fook42/1541-rePico/doc/pictures/IMG_20260502_215122.jpg

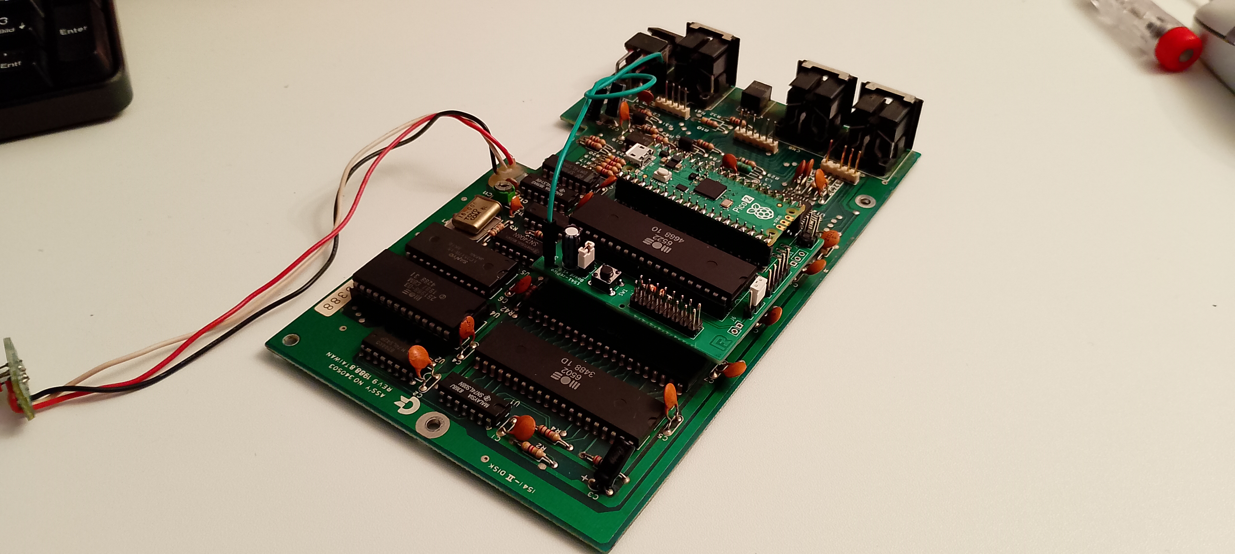
doc/pictures/IMG_20260502_215122.jpg
