fook42/1541-rePico/doc/pictures/1541DiagTest.jpg

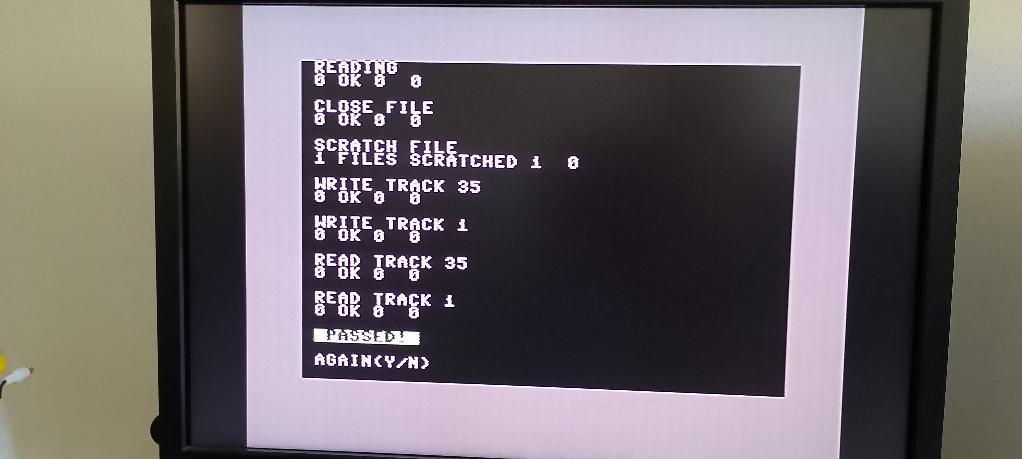
doc/pictures/1541DiagTest.jpg
