fook42/1541-rePico/firmware/SoftwareC64/menu.asm

        ;!to "menu.prg",cbm

        !cpu 6510

;   Typ [8bit, 1 =file, 2=dir], 
;   Filename[chars],stopbyte[8bit, =0] .. jeweils pro eintrag hintereinander
    TYPE_NONE = 0
    TYPE_DIR = 1
    TYPE_D64 = 2
    TYPE_G64 = 3
    TYPE_PRG = 4
    TYPE_UNKNOWN = 255


!ifdef VIC20 {
    MAX_X = 22	    ;screen width
    MAX_LINE = 21


    VIDEORAM = $1000
    COLORRAM = $9400
    E518 = $E55F
    BORDER_COLOR = $04
    SELECTOR_COLOR = $0a
    LOAD = $ffd5
    BA = $ba
    ptr1 = $fb
    ptr2 = $fd
    ptr3 = $f7
    D020 = $900f

} else  { ; VIC20

    MAX_X = 40	    ;screen width
    MAX_LINE = 23

    
!ifdef C16 {
    VIDEORAM = $0c00
    COLORRAM = $0800
    RASTER_LINE = $ff0b
    RASTER_LINE_READ = $ff1d
    VIC_IRQ_ENA = $ff0a
    VIC_IRQ_STATUS = $ff09
    EA31 = $ce0e
    E518 = 55435
    D020 = $ff19
    D021 = $ff15
    BORDER_COLOR = $3b
    SELECTOR_COLOR = $18
    LOAD = $ffd5
    BA = $0137
    ptr1 = $03
    ptr2 = $05
    ptr3 = $9f

} else {
    VIDEORAM = $0400
    COLORRAM = $d800
    RASTER_LINE = $d012
    RASTER_LINE_READ = $d012
    VIC_IRQ_ENA = $d01a
    VIC_IRQ_STATUS = $d019
    EA31 = $ea31
    E518 = $e518
    D020 = $d020
    D021 = $d021
    BORDER_COLOR = $0b
    SELECTOR_COLOR = $02
    BA = $ba
    !ifdef NTSC {
    LOAD = FASTLOAD_EXOS
    } else {
    LOAD = $014b
    }
    ptr1 = $fb
    ptr2 = $fd
    ptr3 = $f7
}
} ; VIC20

    STACK_START = $0138

tmp1 = $02
tmp2 = $ff
directory_end = $ae
x_pos = $92

current_pos = $c1
current_endpos = $c3

current_cursor_position = $9e
!ifdef VIC20 {
current_cursor_last_position = $9f
}

current_index_number = $ac

DRIVECODE_START = $0146

TOGGLE_DISKWRITE_FOR_DISKSWITCH = 2

;CLEANUP_BLOCK_WRITTEN = 1
DRIVE_RESET = 1;
	!ifndef NTSC {
DRIVE_INITIALIZE = 1
	}



LINE_SIZES = $033c  ;"MAX_LINE"-bytes to line lengths


!macro dec_word .x {
        lda .x
        bne +
        dec .x+1
+       dec .x
        }

!macro inc_word .x {
        inc .x
        bne +
        inc .x+1
+
}

!macro conv_to_screen {
        cmp #$5f
        bne +
        lda #$64
        bne .store_code
+
        cmp #$60
        bcc .store_code
        sbc #$20
.store_code:
        }
        ;rts

        !ifdef VIC20 {
        *= $1201
        !by $0b,$12,$00,$00,$9e,$34,$36,$32,$31,$00,$00,$00
        } else {
        !ifndef C16 {
        * = $0808
        } else {
        * = $1008
        }
        }
        jsr fastload_init
        !ifdef VIC20 {
        } else { ; VIC20
        !ifdef C16 {
        lda #$08
        sta BA
        } else {
        dec $01
        }
        } ; VIC20
restart:
        jsr load_menu_file
        !ifdef VIC20 {
        lda #$02
        sta current_cursor_last_position
        }        
        jsr E518
        ldy #MAX_X
-       lda buttomline-1,y
        ora #$80
        sta VIDEORAM+(MAX_LINE+1)*MAX_X-1,y
        lda #BORDER_COLOR
        sta COLORRAM-1,y
        sta COLORRAM+(MAX_LINE+1)*MAX_X-1,y
        dey
        bne -
        !ifdef VIC20 {
        lda #BORDER_COLOR+8
        sta $900f
        } else { ; VIC20
        sta D020
        sty D021
        }
        !ifdef C16 {
        lda #$39
        } else {
        lda #$1b
        sta $d011
        }
        !ifdef VIC20 {
        lda #$c2
        sta $9005
        } else {   ; VIC20
        sta RASTER_LINE
        !ifdef C16 {
        lda #$d5
        sta $ff13
        } else {
        lda #$17
        sta $d018
        lda #$7f
        sta $dc0d
        lda $dc0d
        }
        lda #<irq
        sta $0314
        lda #>irq
        sta $0315
        !ifdef C16 {
        lda #$02
        } else {
        lda #$81
        sta VIC_IRQ_ENA
        }
        !ifdef C16 {
        sta VIC_IRQ_STATUS
        } else {
        inc VIC_IRQ_STATUS
        }
        }  ; VIC20

        ;ldy #<directory_start  ; is zero now
        sty ptr1
        lda #>directory_start
        sta ptr1+1
        sta current_pos+1
-       lda (ptr1),y
        beq end_of_top_line_string
        +conv_to_screen
        ora #$80
        sta VIDEORAM,y
        iny
        cpy #MAX_X
        bne -
        dey
-       iny
        lda (ptr1),y
        bne -
end_of_top_line_string:
        tya
        tax
-       cpx #MAX_X
        bcs end_top_line
        lda #$a0
        sta VIDEORAM,x
        inx
        bne -
end_top_line:
        ;tya
        ;sec
        ;adc #<directory_start
        ;sta current_pos
        iny
        sty  current_pos
        ;lda #$00
        ;adc #>directory_start
        ;lda #>directory_start
        ;sta current_pos+1

        jsr calc_at_current_pos
        ldx tmp1
        stx maxline_cmp_value_calc_sizes
        beq +
        dex
+       stx maxline_cmp_value

repaint:
        jsr print_at_current_pos
        !ifdef VIC20 {
        ldx current_cursor_position
        beq +
        dex
        !byte $89
+       inx
        stx current_cursor_last_position
        }
keyloop:
        !ifdef VIC20 {
        jsr set_scroll_bar
        }
        jsr $ffe4
        beq keyloop
        cmp #17    ;cursor down
        bne no_cursor_down
        lda current_cursor_position
maxline_cmp_value = *+1
        cmp #MAX_LINE-1
        bcc do_cursor_down
        jsr try_scroll_down
        jmp repaint
do_cursor_down:
        inc current_cursor_position
        jmp keyloop

no_cursor_down:
        cmp #145    ;cursor up
        bne no_cursor_up
        lda current_cursor_position
        beq do_scroll_up
        dec current_cursor_position                
        jmp keyloop
do_scroll_up:
        jsr try_scroll_up
        jmp repaint

no_cursor_up:
        cmp #136    ;f7
        bne no_f7
        lda #MAX_LINE
-       pha
        jsr try_scroll_down
        bcc +
        jsr calc_at_current_pos
+       pla
        sec
        sbc #$01
        bne -
        jmp repaint

no_f7:  cmp #133    ;f1
        bne no_f1
        lda #MAX_LINE
-       pha
        jsr try_scroll_up
        bcc +
        jsr calc_at_current_pos
+       pla
        sec
        sbc #$01
        bne -
        jmp repaint

no_f1:  cmp #29     ;cursor right
        bne no_crsr_right
        lda x_pos
        cmp #255-MAX_X
        bcs keyloop
        inc x_pos
        jmp repaint
        
no_crsr_right:
        cmp #157    ;cursor left
        bne no_crsr_left
        lda x_pos
        beq keyloop
        dec x_pos
        jmp repaint
        
no_crsr_left:
        cmp #$13    ; home
        bne no_home
        lda #$00
        sta x_pos
        jmp repaint

no_home:
        cmp #134
        bne no_f3
        !ifdef VIC20 {
        lda #$2c
        sta skip_vic20_fastload
        jmp do_space
        } else { ; VIC20
        !ifdef C16 {
        ldx #$2c
        stx fastload_c16_deactivated
        bne do_space
        } else {
        !ifdef NTSC {
        lda #$24
        sta fix_for_normal_load_ntsc
        bne do_space    ;unconditional	
        } else {
        inc fix_for_normal_load2
        dec fix_for_normal_load3
        lda #$4c
        sta fix_for_normal_load
        lda #<$ffd5 
        sta fix_for_normal_load+1
        lda #>$ffd5 
        sta fix_for_normal_load+2
        bne do_space    ;unconditional
        }
        }
        } ; VIC20
no_f3:       
        cmp #$20
        beq do_space

        cmp #$0d    ;return
        beq do_space
do_keyloop:
        jmp keyloop
do_space:
        sbc #$20
        sta do_run
        jsr get_current_type
        sta current_type
        cmp #TYPE_PRG+1
        bcs do_keyloop
        cmp #TYPE_DIR
        bcc do_keyloop
        lda #$00
        !ifdef VIC20 {
        } else { ; VIC20
        !ifdef C16 {
        lda #$cc
        sta RASTER_LINE
        lda #$02
        sta VIC_IRQ_STATUS
        } else {
        sta VIC_IRQ_ENA
        inc VIC_IRQ_STATUS
        }
        lda #<EA31
        sta $0314
        lda #>EA31
        sta $0315
        !ifdef C16 {
        } else {
        lda #$81
        sta $dc0d
        }
        ;lda $dc0d
        } ; VIC20
        
        lda current_cursor_position
        ;sec        ; carry is set because no "bcc do_keyloop"
        adc current_index_number
        sta index
        lda current_index_number+1
        adc #$00
        sta index+1

        jsr upload_code
        !ifdef CLEANUP_BLOCK_WRITTEN {
        jsr clear_buffer_2
        }
        jsr block_write
        jsr wait_for_flipdisk
        !ifdef VIC20 {
        } else {
        !ifdef DRIVE_RESET {
        jsr drive_initialize
        }
        }
current_type = *+1
        lda #$00
        cmp #TYPE_DIR
        bne +
        jmp restart
+        
        !ifdef C16 {
        sei
        sta $FF3E
        ldx #$ff
        txs
        jsr 55373   ;editor reset
        jsr 62219   ;io init
        jsr 62158   ;restore vectors
        lda #$00
        sta $fdd0 
        cli
        }
do_run = *+1
        lda #$00
        beq do_exit
        !ifdef C16 {
        ;jsr drive_reset
        ;jsr 32814   ;basic reset
fastload_c16_deactivated:
        jsr $0700
        ldx #load_run_text_len
        stx $ef
        } else {
        ldx #load_run_text_len
        stx $c6
        }
        sei
-       lda load_run_text-1,x
        !ifdef C16 {
        sta $0527-1,x
        } else { 
        sta $0277-1,x
        }
        dex
        bne -
do_exit:
        !ifdef VIC20 {
        ldx #$00
        ldy #$00
-       inx
        bne -
        iny
        bne -
        jmp $fd35   ;jump to basic warm start
        } else { ; VIC20
        !ifdef C16 {
        jsr 32962   ;init screen
        cli
        ;jmp ($0302)
        jmp 32778   ;basic warm start
        } else {
        ;lda #$37
        inc $01
        ;jsr $E422
        ;cli
        ;jmp $a474
        jsr $fda3
        jmp $fcf8   ;part of reset, jumps to ($a000)
        }
        } ; VIC20

        !ifndef VIC20 {
irq:    ldy #SELECTOR_COLOR
        !ifndef C16 {
        lda RASTER_LINE_READ
-       cmp RASTER_LINE_READ
        beq -
        }
        sty D021
        lda #<irq2
        sta $0314
        ;lda #>irq2
        ;sta $0315
current_cursor_position_this_irq = *+1
        lda #$00
        clc
        !ifdef C16 {
        adc #$12
        } else {
        adc #$42
        }
        sta RASTER_LINE

        lda current_cursor_position
        asl
        asl
        asl
        sta current_cursor_position_this_irq
        sta current_cursor_position_other_irq
        !ifdef C16 {
        lda #$02
        sta VIC_IRQ_STATUS
        } else {
        inc VIC_IRQ_STATUS
        dec $028B
        bne +
        inc $028B
+
        }
        !ifdef C16 {
        jmp c16irqcont
        } else {
        jmp $ea81
        }

irq2:
        ldy #$03
-       dey
        bne -
        sty D021
        lda #<irq
        sta $0314
        ;lda #>irq
        ;sta $0315
current_cursor_position_other_irq = *+1
        lda #$00
        clc
        !ifdef C16 {
        adc #$a
        } else {
        adc #$39
        }
        sta RASTER_LINE
        !ifdef C16 {
        lda #$02
        sta VIC_IRQ_STATUS
c16irqcont:
        cli
        jsr $DB11       ;tastatur abfragen
        pla
        tay
        pla
        tax
        pla
        rti
        } else {
        inc VIC_IRQ_STATUS
        jmp EA31
        }

    !if >irq2 != >irq {
        !error "irq and irq in different pages"
    }
    }   ;!ifndef VIC20 

get_current_type:
        lda current_pos
        sta ptr1
        lda current_pos+1
        sta ptr1+1
        ldx #$00
        beq get_current_type_loop ;unconditional
--      inx
        ldy #$00
-       iny
        lda (ptr1),y
        bne -
        tya
        sec
        adc ptr1
        sta ptr1
        bcc +
        inc ptr1+1
+
        
get_current_type_loop:
        cpx current_cursor_position
        bne --
        ldy #$00
        lda (ptr1),y
        rts

calc_at_current_pos:
        lda current_pos
        sta ptr1
        lda current_pos+1
        sta ptr1+1
        lda #$00
        sta tmp1
calc_big_loop:
        lda ptr1
        cmp directory_end
        lda ptr1+1
        sbc directory_end+1
        bcs end_calcing

        ldy #$ff
-       iny
        lda (ptr1),y
        bne -
        tya
        sec
        adc ptr1
        sta ptr1
        bcc +
        inc ptr1+1
+
        inc tmp1
        lda tmp1
        cmp #MAX_LINE
        bne calc_big_loop
end_calcing:
        jmp end_printing


print_at_current_pos:
        ;cal line sizes
        lda current_pos
        sta ptr1
        lda current_pos+1
        sta ptr1+1
        ldx #$ff
--      
        ldy #$00
        inx
maxline_cmp_value_calc_sizes = *+1
        cpx #00
        beq print_at_current_pos_continue
        dey
-       iny
        lda (ptr1),y
        bne -
        tya
        sta LINE_SIZES,x
        sec
        adc ptr1
        sta ptr1
        bcc --
        inc ptr1+1
        bne --

print_at_current_pos_continue:        
        ;print
        
        lda #<LINE_SIZES
        sta line_size

        lda current_pos
        sta ptr1
        lda current_pos+1
        sta ptr1+1
        lda #$00
        sta tmp1
        lda #MAX_X
        sta ptr2
        sta ptr3
        lda #>VIDEORAM
        sta ptr2+1
        lda #>COLORRAM
        sta ptr3+1
print_big_loop:
        lda ptr1
        cmp directory_end
        lda ptr1+1
        sbc directory_end+1
        bcc +
        jmp end_printing
+
        ldy #$00
        lax (ptr1),y
        inx
        +inc_word ptr1        

        lda x_pos
line_size = *+1
        cmp LINE_SIZES
        bcc do_print
-       lda (ptr1),y
        beq +
        iny
        bne -
+       sty tmp2
        ldy #$00
        lda #$20
-       sta (ptr2),y
        !ifdef VIC20 {
        lda filetypecolor,x        
        sta (ptr3),y
        lda #$20       
        }
        iny
        cpy #MAX_X
        bne -
        ldy tmp2
        jmp end_line

do_print:
        lda x_pos
        clc
        adc ptr1
        sta ptr1
        bcc +
        inc ptr1+1
+        
-       lda (ptr1),y
        beq string_ends
        +conv_to_screen
        sta (ptr2),y
        lda filetypecolor,x
        sta (ptr3),y
        iny
        cpy #MAX_X
        bne -
        ;find end of string
-       lda (ptr1),y
        beq end_line
        iny
        bne -
        ;!byte $02
string_ends:
        sty tmp2
        lda #$20
-       sta (ptr2),y
        !ifdef VIC20 {
        lda filetypecolor,x        
        sta (ptr3),y
        lda #$20       
        }
        iny
        cpy #MAX_X
        bne -
        ldy tmp2
end_line:
        tya
        sec
        adc ptr1
        sta ptr1
        bcc +
        inc ptr1+1
        clc
+       lda ptr2
        adc #MAX_X
        sta ptr2
        sta ptr3
        bcc +
        inc ptr2+1
        inc ptr3+1
+       inc line_size
        inc tmp1
        lda tmp1
        cmp #MAX_LINE
        beq end_printing
        jmp print_big_loop
end_printing:
        lda ptr1
        sta current_endpos
        lda ptr1+1
        sta current_endpos+1
        rts

!macro current_pos_equ_ptr1_plus_1 {
        lax ptr1
        sbx #$100-$01
        stx current_pos
        lda ptr1+1
        adc #$00
        sta current_pos+1
        }

try_scroll_up:
        lda current_index_number
        ora current_index_number+1
        beq try_scroll_up_failed
        lax current_pos
        sbx #$02
        stx ptr1
        lda current_pos+1
        sbc #$00
        sta ptr1+1
        ldy #$00
        jmp try_scroll_up_do_search
-
        +dec_word ptr1
try_scroll_up_do_search:
        lda (ptr1),y
        bne -
        +current_pos_equ_ptr1_plus_1
        +dec_word current_index_number
        sec
        rts
        
try_scroll_down_failed:
try_scroll_up_failed:
        clc
        rts


try_scroll_down:
        lda current_endpos
        cmp directory_end
        lda current_endpos+1
        sbc directory_end+1
        bcs try_scroll_down_failed
        lda current_pos
        sta ptr1
        lda current_pos+1
        sta ptr1+1
        ldy #$00
        beq try_scroll_down_do_search   ;unconditional
-       
        +inc_word ptr1
try_scroll_down_do_search:
        lda (ptr1),y
        bne -
        +current_pos_equ_ptr1_plus_1
        +inc_word current_index_number
        sec
ret_vic20:
        rts


        !ifdef VIC20 {
set_scroll_bar:
        ldx current_cursor_last_position
        cpx current_cursor_position
        beq ret_vic20
        jsr get_curser_ptr1
        ldy #22-1
-       lda (ptr1),y
        and #$7f
        sta (ptr1),y
        dey
        bpl -
        
        ldx current_cursor_position
        stx current_cursor_last_position
        jsr get_curser_ptr1
        ldy #22-1
-       lda (ptr1),y
        ora #$80
        sta (ptr1),y
        dey
        bpl -         
        rts
        
get_curser_ptr1:
        lda screen_low_bytes,x
        sta ptr1
        lda screen_high_bytes,x
        sta ptr1+1
        rts


screen_low_bytes:
        !for i,1,22 {
        !byte <(VIDEORAM+22*i)
        }
 
screen_high_bytes:
        !for i,1,22 {
        !byte >(VIDEORAM+22*i)
        }
        

        }


load_menu_file:
        !ifdef VIC20 {
        jsr L1476   ;initialize
        jsr L14DC   ;execute fastloader
        ldx #<directory_start
        ldy #>directory_start
        lda #$05
        sec
        jsr vicload
        ldx L16A0+1
        ldy L16A0+2
        stx directory_end
        sty directory_end+1
        lda #$ff
        jsr vicload
        } else { ; VIC20
        lda #fname_end-fname
        ldx #<fname
        ldy #>fname
        jsr $ffbd     ; call SETNAM
        lda #$01
        ldx BA
        ldy #$00      ; $00 means: load to new address
        jsr $ffba     ; call SETLFS

        ;ldx #<directory_start
        ldy #>directory_start
        ;lda #$00      ; $00 means: load to memory (not verify)
        lxa #$00
        stx $c3
        sty $c4
        jsr LOAD      ; call LOAD
        bcs .error    ; if carry set, a load error has happened
        !ifdef C16 {
        stx directory_end
        sty directory_end+1
        }
        } ; VIC20
        lda #$00
        sta current_index_number
        sta current_index_number+1
        sta current_cursor_position
        sta x_pos
        rts

.error
        ; Accumulator contains BASIC error code

        ; most likely errors:
        ; A = $05 (DEVICE NOT PRESENT)
        ; A = $04 (FILE NOT FOUND)
        ; A = $1D (LOAD ERROR)
        ; A = $00 (BREAK, RUN/STOP has been pressed during loading)

        ;... error handling ...
-       inc D020
        jmp -
    
block_write:
        ; open the channel file

        LDA #cname_end-cname
        LDX #<cname
        LDY #>cname
        JSR $FFBD     ; call SETNAM

        LDA #$02      ; file number 2
        ldx BA
        tay           ; secondary address 2
        JSR $FFBA     ; call SETLFS

        JSR $FFC0     ; call OPEN
        BCS .error    ; if carry set, the file could not be opened

        ; open the command channel

        LDA #bpcmd_end-bpcmd
        LDX #<bpcmd
        LDY #>bpcmd
        JSR $FFBD     ; call SETNAM
        LDA #$0F      ; file number 15
        ldx BA
        tay           ; secondary address 15
        JSR $FFBA     ; call SETLFS

        jsr $FFC0     ; call OPEN (open command channel and send B-P command)
        BCS error    ; if carry set, the file could not be opened

        ; check drive error channel here to test for
        ; FILE NOT FOUND error etc.

        LDX #$02      ; filenumber 2
        JSR $FFC9     ; call CHKOUT (file 2 now used as output)

        LDY #$00
.loop   LDA sector_address,Y   ; read byte from memory
        JSR $FFD2     ; call CHROUT (write byte to channel buffer)
        INY
        cpy #sector_len
        BNE .loop     ; next byte, end when 256 bytes are read

        LDX #$0F      ; filenumber 15
        JSR $FFC9     ; call CHKOUT (file 15 now used as output)

        LDY #$00
.loop2  LDA bwcmd,Y   ; read byte from command string
        JSR $FFD2     ; call CHROUT (write byte to command channel)
        INY
        CPY #bwcmd_end-bwcmd
        BNE .loop2    ; next byte, end when 256 bytes are read
.close

        JSR $FFCC     ; call CLRCHN

        LDA #$0F      ; filenumber 15
        JSR $FFC3     ; call CLOSE

        LDA #$02      ; filenumber 2
        JSR $FFC3     ; call CLOSE

        JMP $FFCC     ; call CLRCHN

error:
        ; Akkumulator contains BASIC error code

        ; most likely errors:
        ; A = $05 (DEVICE NOT PRESENT)

        ;... error handling for open errors ...
        JMP .close    ; even if OPEN failed, the file has to be closed

drive_initialize:
        !ifdef DRIVE_INITIALIZE {
        !ifndef C16 {
        lda do_run
        bpl drive_reset
        }
        lda #drive_init_end-drive_init
        ldx #<drive_init
        ldy #>drive_init
        bne execute_code_cont ;unconditional 
	} else {
	lda do_run
	beq drive_reset
	rts		;for EXOS, no initialize
	}
	!ifdef DRIVE_RESET {
drive_reset:
        lda #$60
        sta reset_activated
        ldx #<drive_fffc
        ;ldy #>drive_fffc
        bne execute_code ;unconditional
        }
                

wait_for_flipdisk:
        ldx #<wait_for_diskchange
        ;ldy #>wait_for_diskchange
        !ifdef CLEANUP_BLOCK_WRITTEN {
        bne execute_code ;unconditional

clear_buffer_2:
        ldx #<clear_buffer2
        ;ldy #>clear_buffer2
        } 

execute_code:
        ;in x/y code (x low)
        stx me_dest
        ;sty me_dest+1
        lda #me_comm_end-me_comm
        ldx #<me_comm
        ldy #>me_comm
        bne execute_code_cont

upload_code:
        ; open the command channel

        LDA #mw_end-mw_comm
        LDX #<mw_comm
        LDY #>mw_comm
execute_code_cont:
        JSR $FFBD     ; call SETNAM
        LDA #$0F      ; file number 15
        ldx BA
        tay           ; secondary address 15
        JSR $FFBA     ; call SETLFS

        jsr $FFC0     ; call OPEN (open command channel and send B-P command)
        BCS error     ; if carry set, the file could not be opened
reset_activated:
        LDA #$0F      ; filenumber 15
        jsr $FFC3     ; call CLOSE
        JMP $FFCC     ; call CLRCHN

me_comm:
         !text "M-E"
me_dest:
         !byte <DRIVECODE_START
         !byte >DRIVECODE_START
me_comm_end:

cname:  !text "#"
cname_end:

bpcmd:  !text "B-P:2 0"
bpcmd_end:

bwcmd:  !text "U2:2 0 18 2"
        !BYTE $0D     ; carriage return, required to start command
bwcmd_end:

        !ifdef DRIVE_INITIALIZE {
drive_init:
        !text "I"
drive_init_end:
        }

fname:  !text "DATAFILE"
fname_end:
       
load_run_text:
        !byte 'S'
        !byte 'y'
        !byte '3'
        !byte '1'
        !byte '2'
        !byte $0d
        !byte 'R'
        !byte 'u'
        !byte $0d
load_run_text_len = *-load_run_text

buttomline:
        !ifdef VIC20 {
        !scr "<SPC>=mnt <ret/F3>=run"
        } else { ; VIC20
        !ifdef C16 {
        !scr "<SPC>=mnt <ret/F2>=run F1=pgup HLP=pgdwn"
        } else {
        !scr "<SPC>=mnt <ret/F3>=run  F1=pgup F7=pgdwn"
        }
        } ; VIC20

mw_comm:
         !text "M-W"
mw_dest: !word DRIVECODE_START
         !byte diskdrive_code_len
diskdrive_code:
        !pseudopc DRIVECODE_START {
        !ifdef CLEANUP_BLOCK_WRITTEN {
clear_buffer2:
        lxa #$00
-       sta $0600,x
        inx
        bne -
        rts
        }
wait_for_diskchange:
        !if TOGGLE_DISKWRITE_FOR_DISKSWITCH > 1 {
        ldx #TOGGLE_DISKWRITE_FOR_DISKSWITCH
        }
--
-       lda $1c00
        and #$10
        bne -
-       lda $1c00
        and #$10
        beq -
        !if TOGGLE_DISKWRITE_FOR_DISKSWITCH > 1 {
        dex
        bne --
        }
        rts
        
drive_fffc:
        jmp ($fffc)
        }
diskdrive_code_len = * - diskdrive_code
mw_end:

filetypecolor:
    !ifdef VIC20 {
        !byte $02   ; unknown
        !byte $02   ; none
        !byte $05   ; dir
        !byte $03   ; d64
        !byte $03   ; g64
        !byte $01   ; prg

L1476:  LDA $ba
        JSR LISTEN
        LDA #$6F
        JSR SECOND
        LDA #$49
        JSR CIOUT
        JSR UNLSN
        RTS


L14DC:  LDA $ba
        JSR LISTEN
        LDA #$6F
        JSR SECOND
        LDX #$00
L14E8:  LDA L14FD,X
        JSR CIOUT
        INX
        CPX #$05
        BNE L14E8
        JSR UNLSN

        ;LDA #$02
        LDY #$00
        LDX #$00
L1425:  DEX
        BNE L1425
        DEY
        BNE L1425
        ;SEC
        ;SBC #$01
        ;BNE L1425

        RTS

L14FD:  !byte $4D,$2D,$45,<L041A, >L041A


    } else { ; VIC20
    !ifdef C16 {
        !byte $52   ; unknown
        !byte $52   ; none
        !byte $5e   ; dir
        !byte $53   ; d64
        !byte $43   ; g64
        !byte $51   ; prg
    } else {
        !byte $0a   ; unknown
        !byte $0a   ; none
        !byte $0e   ; dir
        !byte $03   ; d64
        !byte $03   ; g64
        !byte $0f   ; prg
    }
    } ; VIC20

sector_address:
index:  !word 0
        !ifdef CLEANUP_BLOCK_WRITTEN {
        !text "MENU"
        }
sector_len = * - sector_address


directory_start = (*+$ff) & $ff00

        ;all stuff after this is erased
        ;by loading "DATAFILE"

        !ifdef VIC20 {
fastload_init:
        ldx #fastload_stack_len
-       lda fastload_stack-1,x
        sta STACK_START-1,x
        dex
        bne -
        lda #>vicload
        !src "vic20loader.asm"

fastload_stack:
!pseudopc STACK_START {
skip_vic20_fastload:
        jmp do_vic_fastload
        lda #load_star_name_len
        ldx #<load_star_name
        ldy #>load_star_name
        jsr $ffbd     ; call SETNAM
        lda #$01
        ldx BA
        tay           ; $01 means: load to origin address
        jsr $ffba     ; call SETLFS
        lda #$00
        jsr $ffd5
        lda $ae
        sta $2d
        lda $af
        sta $2e
        rts        
load_star_name:
        !text ":*"
load_star_name_len = * - load_star_name

do_vic_fastload:
        jsr L1476   ;initialize
        jsr L14DC   ;execute fastloader
        lda #$00    ; file #0
        clc
        jmp vicload
        ;!byte $02
}
fastload_stack_len = * - fastload_stack 

        rts
        

        } else { ;VIC20
        !ifdef C16 {
;;;;;;;;;;;;;;;;;;; PLUS4 START ;;;;;;;;;;;;;;;;;;;;;;;
c16keyb:
        !byte 133,134,135,136,133,134,135,136
        
fastload_init:
        ldx #$07
fkey_clear_loop:
        lda #$01
        sta $055f,x
        lda c16keyb,x
        sta $0567,x
        dey
        dex
        bpl fkey_clear_loop 

        php
        sei
        sta $ff3f
        ldy #>(fastload_main_len+$ff)
        ldx #$00
-       
src = *+1
        lda fastload_main,x
dst = *+1
        sta $f300,x
        inx
        bne -
        inc src+1
        inc dst+1
        dey
        bne -
        sta $ff3e
        
        ldx #fastload_stack_len
-       lda fastload_stack-1,x
        sta STACK_START-1,x
        dex
        bne -

        ldx #fastload_0700_len
-       lda fastload_0700-1,x
        sta $0700-1,x
        dex
        bne -
        ;for VICE tests
        ;lda #$60
        ;sta $0700
        jsr $0700
        plp
        rts

fastload_main:
        !bin "fastload_16_f300.bin",,2
fastload_main_len = *-fastload_main

fastload_0700:
        !bin "fastload_16_0700.bin",,2
fastload_0700_len = *-fastload_0700
fastload_stack:
!pseudopc STACK_START {
load_fast:
        lda #load_star_name_len
        ldx #<load_star_name
        ldy #>load_star_name
        jsr $ffbd     ; call SETNAM
        lda #$01
        ldx BA
        tay           ; $01 means: load to origin address
        jsr $ffba     ; call SETLFS

        lda #$00
        cli
        jsr LOAD
        bcs +         ; if carry set, a load error has happened
        stx $2d
        sty $2e
+
        jsr 62158       ;restore vectors
        anc #0
        rts
load_star_name:
        !text ":*"
load_star_name_len = * - load_star_name
}
fastload_stack_len = *-fastload_stack

;;;;;;;;;;;;;;;;;;; PLUS4 END ;;;;;;;;;;;;;;;;;;;;;;;

        } else {

        !ifdef NTSC {
;;;;;;;;;;;;;;;;;;; NTSC C64 START ;;;;;;;;;;;;;;;;;;;;;;;

fastload_init:
        ldx #fastload_stack_len
-       lda fastload_stack-1,x
        sta STACK_START-1,x
        dex
        bne -
        !src "exos_ntsc.asm"

fastload_stack:
!pseudopc STACK_START {
        lda #load_star_name_len
        ldx #<load_star_name
        ldy #>load_star_name
        jsr $ffbd     ; call SETNAM
        lda #$01
        ldx BA
        tay           ; $01 means: load to origin address
        jsr $ffba     ; call SETLFS
FASTLOAD_EXOS:
        lda $01
        pha
        lda #$35
fix_for_normal_load_ntsc:
        sta $01
        lda #$00
        jsr $ffd5
        lda $ae
        sta $2d
        lda $af
        sta $2e
        pla
        sta $01
        cli
        rts        
load_star_name:
        !text ":*"
load_star_name_len = * - load_star_name
}
fastload_stack_len = * - fastload_stack 

;;;;;;;;;;;;;;;;;;; NTSC C64 END ;;;;;;;;;;;;;;;;;;;;;;;
     
        } else {

;;;;;;;;;;;;;;;;;;; PAL C64 START ;;;;;;;;;;;;;;;;;;;;;;;

fastload_init:
        ldx #fastload_stack_len
-       lda fastload_stack-1,x
        sta STACK_START-1,x
        dex
        bne -
        ldy #>(fastload_main_len)
-       
fastload_main_src_ptr = *+2
        lda fastload_main,x
fastload_main_dst_ptr = *+2
        sta $e000,x
        inx
        bne -
        inc fastload_main_src_ptr
        inc fastload_main_dst_ptr
        dey
        bpl -
        rts

fastload_stack:
!pseudopc STACK_START {
fix_for_normal_load2 = *+1
        lda #load_star_name_len-1
fix_for_normal_load3 = *+1
        ldx #<load_star_name+1
        ldy #>load_star_name
        jsr $ffbd     ; call SETNAM
        lda #$01
        ldx BA
        tay           ; $01 means: load to origin address
        jsr $ffba     ; call SETLFS

        lda #$00
fix_for_normal_load:
        !bin "fastload_0140.bin",$2c,2+11
        jmp $f5a9
        !bin "fastload_0140.bin",,2+11+$2f
load_star_name:     ; bug in fast loader : cannot handle ":*"
        !text ":*"
load_star_name_len = * - load_star_name
        }
fastload_stack_len = * - fastload_stack      

fastload_main:
        !bin "fastload_e000.bin",,2
fastload_main_len = *-1
        }
        ;;;;;;;;;;;;;;;;;;; PAL C64 END ;;;;;;;;;;;;;;;;;;;;;;;

        }
        }   ;VIC20
