fook42/1541-rePico/firmware/SoftwareC64/exos_ntsc.asm

; ---------------------------------------------------------------------------
; exos_ntsc.asm - disassembly of exos_ntsc.prg, reassembles byte-identical
;                 with ACME (acme -o exos_ntsc.prg exos_ntsc.asm)
;
; --- $080d: relocator / block-copy routine -----------------------------
relocate:
        lda #$00
        sta $57
        sta $59
        lda #>$e000
        sta $58
        lda #>$a000
        sta $5a        
        lda #<packed_data
        sta $5b
        lda #>packed_data
        sta $5c
        ldy #$00
copy8k:
        lda ($57),y
        sta ($57),y
        lda ($59),y
        sta ($59),y
        iny
        bne copy8k
        inc $5a
        inc $58
        bne copy8k

blocktab:
        ldy #$00
        lda ($5b),y
        sta $59
        iny
        lda ($5b),y
        beq relocate_done
        sta $5a
        iny
        lda ($5b),y
        tay
        sta $fc
        clc
        lda $5b
        adc #$03
        sta $5b
        lda $5c
        adc #$00
        sta $5c
copyblk:
        dey
        lda ($5b),y
        sta ($59),y
        tya
        bne copyblk
        clc
        lda $5b
        adc $fc
        sta $5b
        lda $5c
        adc #$00
        sta $5c
        bcc blocktab
relocate_done:
        rts

packed_data:
; --- $086d: packed relocation-block table (not code) --------------------
; format per block: dest_word (lo/hi+$c0), length (0 = 256), then <length> data bytes
; table ends with a $00 dest_hi byte
;block_01  ; dest=$e1da len=1 (@ $086d)
;        !word $e1da
;        !byte $01
;        !byte $08
;block_02  ; dest=$e1dc len=1 (@ $0871)
;        !word $e1dc
;        !byte $01
;        !byte $01
;block_03  ; dest=$e47c len=25 (@ $0875)
;        !word $e47c
;        !byte $19
;        !byte $20,$43,$36,$34,$20,$49,$4d,$50,$52,$4f,$56,$45,$44,$20,$42,$59
;        !byte $20,$45,$58,$4f,$53,$20,$56,$33,$20
;block_04  ; dest=$e49b len=3 (@ $0891)
;        !word $e49b
;        !byte $03
;        !byte $20,$42,$59
;block_05  ; dest=$e49f len=8 (@ $0897)
;        !word $e49f
;        !byte $08
;        !byte $4a,$2e,$53,$43,$48,$45,$4d,$4d
;block_06  ; dest=$e4a8 len=1 (@ $08a2)
;        !word $e4a8
;        !byte $01
;        !byte $4c
;block_07  ; dest=$e535 len=1 (@ $08a6)
;        !word $e535
;        !byte $01
;        !byte $0f
;block_08  ; dest=$e5e8 len=2 (@ $08aa)
;        !word $e5e8
;        !byte $02
;        !byte $c9,$fb			;eliminate $fbc9 also ?
;block_09  ; dest=$e5ee len=3 (@ $08af)
;        !word $e5ee
;        !byte $03
;        !byte $20,$eb,$f0		;eliminate $f0eb also ?
;block_10  ; dest=$e5f4 len=2 (@ $08b5)
;        !word $e5f4
;        !byte $02
;        !byte $ff,$f0			;eliminate $f0ff also ?
;block_11  ; dest=$e935 len=3 (@ $08ba)
;        !word $e935
;        !byte $03
;        !byte $20,$b8,$fc		;eliminate $fcb8 also ?
;block_12  ; dest=$e94c len=1 (@ $08c0)
;        !word $e94c
;        !byte $01
;        !byte $20
;block_13  ; dest=$ea15 len=1 (@ $08c4)
;        !word $ea15
;        !byte $01
;        !byte $01
;block_14  ; dest=$eb1d len=1 (@ $08c8)
;        !word $eb1d
;        !byte $01
;        !byte $03
;block_15  ; dest=$ec06 len=4 (@ $08cc)
;        !word $ec06
;        !byte $04
;        !byte $e3,$e0,$e1,$e2
;block_16  ; dest=$ec7b len=4 (@ $08d3)
;        !word $ec7b
;        !byte $04
;        !byte $e7,$e4,$e5,$e6
;block_17  ; dest=$ecd9 len=2 (@ $08da)
;        !word $ecd9
;        !byte $02
;        !byte $00,$00
;block_18  ; dest=$eebb len=41 (@ $08df)
;        !word $eebb
;        !byte $29
;        !byte $78,$84,$01,$a6,$5c,$b1,$5d,$91,$5f,$c8,$d0,$f9,$e6,$5e,$e6,$60
;        !byte $ca,$d0,$f2,$a9,$37,$85,$01,$58,$60,$78,$84,$01,$a6,$5c,$b1,$5d
;        !byte $48,$b1,$5f,$91,$5d,$68,$91,$5f,$c8
;block_19  ; dest=$eee5 len=116 (@ $090b)
;        !word $eee5
;        !byte $74
;        !byte $f3,$e6,$5e,$e6,$60,$ca,$d0,$ec,$a9,$37,$85,$01,$58,$60,$c9,$e4
;        !byte $90,$14,$c9,$e8,$b0,$3d,$38,$e9,$e4,$0a,$0a,$18,$69,$a0,$85,$60
;        !byte $20,$2b,$ef,$4c,$a2,$fc,$c9,$e0,$90,$29,$20,$2b,$ef,$aa,$bd,$47
;        !byte $ee,$e0,$e2,$b0,$04,$85,$60,$d0,$06,$85,$5e,$a9,$04,$85,$60,$4c
;        !byte $94,$fc,$a8,$ac,$a8,$ac,$a0,$00,$84,$5d,$84,$5f,$a2,$04,$86,$5e
;        !byte $86,$5c,$60,$c9,$16,$d0,$09,$20,$72,$ef,$20,$a2,$fc,$4c,$6a,$ef
;        !byte $c9,$17,$d0,$06,$20,$72,$ef,$4c,$94,$fc,$c9,$0c,$18,$d0,$3c,$20
;        !byte $72,$ef,$a5,$5d
;block_20  ; dest=$ef5a len=90 (@ $0982)
;        !word $ef5a
;        !byte $5a
;        !byte $5f,$85,$5f,$86,$5d,$a5,$5e,$a6,$60,$85,$60,$86,$5e,$20,$94,$fc
;        !byte $a9,$0f,$8d,$77,$02,$e6,$c6,$60,$a9,$00,$85,$5f,$a5,$2b,$a6,$2c
;        !byte $85,$5d,$86,$5e,$a2,$ff,$e8,$bd,$aa,$ef,$20,$d2,$ff,$d0,$f7,$20
;        !byte $42,$f1,$f0,$fb,$c9,$30,$90,$60,$c9,$34,$b0,$5c,$20,$d2,$ff,$aa
;        !byte $a9,$0d,$20,$d2,$ff,$bd,$ba,$ef,$85,$5c,$bd,$be,$ef,$85,$60,$60
;        !byte $0d,$3c,$12,$30,$92,$3e,$20,$32,$30,$4b
;block_21  ; dest=$efb5 len=151 (@ $09df)
;        !word $efb5
;        !byte $97
;        !byte $42,$30,$2d,$46,$46,$0d,$3c,$12,$31,$92,$3e,$20,$34,$4b,$20,$42
;        !byte $30,$2d,$42,$46,$0d,$3c,$12,$32,$92,$3e,$20,$34,$4b,$20,$43,$30
;        !byte $2d,$43,$46,$0d,$3c,$12,$33,$92,$3e,$20,$31,$32,$4b,$20,$44,$30
;        !byte $2d,$46,$46,$0d,$00,$50,$10,$10,$30,$b0,$b0,$c0,$d0,$c9,$18,$d0
;        !byte $06,$20,$34,$f0,$4c,$c3,$a6,$c9,$1a,$d0,$41,$20,$34,$f0,$a2,$32
;        !byte $c6,$60,$a0,$fd,$b1,$5f,$f0,$03,$88,$d0,$f9,$c8,$84,$5e,$18,$a5
;        !byte $5f,$65,$5e,$85,$5f,$a5,$60,$69,$00,$85,$60,$c5,$2c,$f0,$06,$ca
;        !byte $d0,$de,$4c,$c3,$a6,$a5,$2b,$85,$5f,$a5,$2c,$85,$60,$d0,$f3,$c6
;        !byte $60,$a0,$ff,$b1,$5f,$08,$e6,$60,$28,$d0,$ea,$60,$c9,$06,$d0,$03
;        !byte $4c,$32,$f7,$aa,$68,$68,$8a
;block_22  ; dest=$f04d len=85 (@ $0a79)
;        !word $f04d
;        !byte $55
;        !byte $20,$20,$20,$8a,$53,$d9,$34,$30,$39,$36,$2a,$31,$32,$9d,$00,$9d
;        !byte $85,$93,$4c,$c9,$00,$0d,$86,$52,$55,$4e,$3a,$00,$0d,$8c,$43,$4c
;        !byte $cf,$37,$3a,$4f,$d0,$37,$2c,$38,$2c,$31,$35,$2c,$22,$22,$00,$14
;        !byte $87,$4c,$4f,$41,$44,$22,$22,$00,$14,$8b,$53,$41,$56,$45,$22,$22
;        !byte $00,$14,$89,$53,$d9,$33,$32,$37,$36,$38,$00,$0d,$88,$93,$4c,$cf
;        !byte $22,$24,$22,$2c,$38
;block_23  ; dest=$f0a3 len=1 (@ $0ad1)
;        !word $f0a3
;        !byte $01
;        !byte $0d
;block_24  ; dest=$f0d9 len=23 (@ $0ad5)
;        !word $f0d9
;        !byte $17
;        !byte $4c,$cf,$22,$3a,$2a,$22,$2c,$38,$2c,$31,$3a,$58,$20,$08,$f9,$4c
;        !byte $28,$f5,$a2,$00,$bd,$d8,$f0
;block_25  ; dest=$f0f1 len=21 (@ $0aef)
;        !word $f0f1
;        !byte $15
;        !byte $d2,$ff,$e8,$e0,$0c,$d0,$f5,$a2,$06,$78,$60,$ea,$ff,$ff,$ff,$0d
;        !byte $52,$55,$4e,$3a,$0d
;block_26  ; dest=$f387 len=1 (@ $0b07)
;        !word $f387
;        !byte $01
;        !byte $08			;skip tape devices
;block_27  ; dest=$f389 len=2 (@ $0b0b)
;        !word $f389
;        !byte $02
;        !byte $90,$f3
;block_28  ; dest=$f409 len=61 (@ $0b10)
;        !word $f409
;        !byte $3d
;        !byte $60,$20,$20,$f4,$d0,$03,$a9,$ff,$60,$4c,$02,$fd,$ea,$20,$20,$f4
;        !byte $d0,$f7,$68,$68,$4c,$66,$fe,$a2,$00,$8e,$03,$dc,$ca,$8e,$02,$dc
;        !byte $a9,$7f,$8d,$00,$dc,$ad,$01,$dc,$c9,$fb,$60,$a5,$00,$29,$3f,$85
;        !byte $00,$6c,$00,$a0,$a5,$00,$29,$3f,$85,$00,$6c,$02,$a0
;block_29  ; dest=$f4b7 len=1 (@ $0b50)
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
        !byte $01,$20,$ed,$f5,$a9,$37,$85,$01,$60,$c9,$01,$d0,$07,$a5,$00,$09
        !byte $40,$85,$00,$60,$c9,$0b,$d0,$29,$a9,$06,$a2,$08,$a0,$0f,$20,$ba
        !byte $ff,$a9,$00,$20,$bd,$ff,$20,$c0,$ff,$a2,$06,$20,$c6,$ff
block_58  ; dest=$fc7f len=9 (@ $10e8)
        !word $fc7f
        !byte $09
        !byte $cf,$ff,$20,$d2,$ff,$24,$90,$50,$f6
block_59  ; dest=$fc89 len=58 (@ $10f4)
        !word $fc89
        !byte $3a
        !byte $cc,$ff,$a9,$06,$20,$c3,$ff,$60,$4c,$f3,$ee,$a0,$20,$b9,$ba,$ee
        !byte $99,$09,$02,$88,$d0,$f7,$4c,$0a,$02,$a0,$20,$b9,$d3,$ee,$99,$09
        !byte $02,$88,$d0,$f7,$4c,$0a,$02,$f7,$4c,$0a,$02,$00,$00,$00,$00,$ee
        !byte $a5,$02,$ad,$8d,$02,$29,$02,$d0,$f9,$60
block_60  ; dest=$fce8 len=2 (@ $1131)
        !word $fce8
        !byte $02
        !byte $0a,$f4
;block_61  ; dest=$fcff len=3 (@ $1136)
;        !word $fcff
;        !byte $03
;        !byte $4c,$34,$f4
;block_62  ; dest=$fd68 len=36 (@ $113c)
;        !word $fd68
;        !byte $24
;        !byte $ad,$ff,$9f,$a2,$ff,$8e,$ff,$9f,$ec,$ff,$9f,$d0,$10,$e8,$8e,$ff
;        !byte $9f,$ec,$ff,$9f,$d0,$07,$8d,$ff,$9f,$a0,$a0,$d0,$07,$8d,$ff,$9f
;        !byte $a0,$80,$a2,$00
;block_63  ; dest=$fe57 len=2 (@ $1163)
;        !word $fe57
;        !byte $02
;        !byte $16,$f4
;block_64  ; dest=$fe6f len=3 (@ $1168)
;        !word $fe6f
;        !byte $03
;        !byte $4c,$3d,$f4
;block_65  ; dest=$ff00 len=1 (@ $116e)
;        !word $ff00
;        !byte $01
;        !byte $df
blocktab_end  ; @ $1172
        !byte $00,$00,$00,$00,$00
