fook42/1541-rePico/firmware/src/menu.c

/* menu structure handling */

// taken over from 1541-rebuild from Th.Kattanek

// last change: 31/10/2025

#include "menu.h"
#include "display.h"
#include "gui_constants.h"

static MENU_STRUCT *current_menu;

void menu_init(MENU_STRUCT* menu, MENU_ENTRY *menu_entrys, const uint8_t menu_entry_count, const uint8_t lcd_col_count, const uint8_t lcd_row_count)
{
    menu->entry_list = menu_entrys;
    menu->entry_count = menu_entry_count;
    menu->lcd_col_count = lcd_col_count;
    menu->lcd_row_count = lcd_row_count;

    menu->pos = 0;
    menu->lcd_cursor_pos = 0;
    menu->lcd_window_pos = 0;

    menu->lcd_cursor_char    = display_pointer_char;  // 126 Standard Pfeil
    menu->lcd_more_top_char  = display_more_top_char;
    menu->lcd_more_down_char = display_more_down_char;

    menu->view_obsolete = 1;
}

void menu_set_root(MENU_STRUCT *menu)
{
    current_menu = menu;
}

uint16_t menu_update(const uint8_t key_code)
{
    uint8_t command = MC_NO_COMMAND;
    uint8_t value = 0x00;

    switch(key_code)
    {
        case KEY0_DOWN:
            {
                if(current_menu->lcd_cursor_pos > 0)
                {
                    current_menu->lcd_cursor_pos--;
                    current_menu->view_obsolete = 1;
                    command = MC_CHANGE_ENTRY;
                    value = current_menu->entry_list[current_menu->lcd_window_pos + current_menu->lcd_cursor_pos].id;
                }
                else
                {
                    if(current_menu->lcd_window_pos > 0)
                    {
                        current_menu->lcd_window_pos--;
                        current_menu->view_obsolete = 1;
                        command = MC_CHANGE_ENTRY;
                        value = current_menu->entry_list[current_menu->lcd_window_pos + current_menu->lcd_cursor_pos].id;
                    }
                }
            }
            break;

        case KEY1_DOWN:
            {
                if(    (current_menu->lcd_cursor_pos < (current_menu->lcd_row_count-1))
                    && (current_menu->lcd_cursor_pos < (current_menu->entry_count-1)))
                {
                    current_menu->lcd_cursor_pos++;
                    current_menu->view_obsolete = 1;
                    command = MC_CHANGE_ENTRY;
                    value = current_menu->entry_list[current_menu->lcd_window_pos + current_menu->lcd_cursor_pos].id;
                }
                else
                {
                    if(current_menu->lcd_window_pos < (current_menu->entry_count - current_menu->lcd_row_count))
                    {
                        current_menu->lcd_window_pos++;
                        current_menu->view_obsolete = 1;
                        command = MC_CHANGE_ENTRY;
                        value = current_menu->entry_list[current_menu->lcd_window_pos + current_menu->lcd_cursor_pos].id;
                    }
                }
            }
            break;

        case KEY2_UP:
            {
                // menu->lcd_window_pos + menu->lcd_cursor_pos = index in MenuEntryList
                command = MC_SELECT_ENTRY;
                uint8_t menu_index = current_menu->lcd_window_pos + current_menu->lcd_cursor_pos;
                value = current_menu->entry_list[menu_index].id;

                switch (current_menu->entry_list[menu_index].type)
                {
                    case ENTRY_MENU:
                        current_menu->entry_list[menu_index].menu->parent_menu = current_menu;
                        current_menu = current_menu->entry_list[menu_index].menu;
                        current_menu->lcd_cursor_pos = 1;
                        current_menu->view_obsolete = 1;
                        break;

                    case ENTRY_TO_PARENT:
                        current_menu = current_menu->parent_menu;
                        current_menu->view_obsolete = 1;
                        break;

                    case ENTRY_ONOFF:
                    case ENTRY_BOOL:
                    case ENTRY_BIN:
                        current_menu->entry_list[menu_index].var1 ^= 1;
                        current_menu->entry_list[menu_index].var1 &= 1;
                        break;

                    default:
                        break;
                }
            }
            break;

        case KEY2_TIMEOUT1:
            {
                if(current_menu->parent_menu != 0)
                {
                    current_menu = current_menu->parent_menu;
                    current_menu->view_obsolete = 1;
                }
                else
                {
                    command = MC_EXIT_MENU;
                }
            }
            break;

        case KEY2_TIMEOUT2:
            break;

        default:
            break;
    }

    if(current_menu->view_obsolete)
    {
        current_menu->view_obsolete = 0;

        menu_refresh();
    }

    return (((uint16_t) command) << 8 | value);
}

void menu_refresh()
{
    // Menu Neu Zeichnen
    display_clear();

    for(int i=0; (i<current_menu->lcd_row_count) && (i<current_menu->entry_count); i++)
    {
        display_setcursor(1,i);
        display_string(current_menu->entry_list[i+current_menu->lcd_window_pos].name);

        switch(current_menu->entry_list[i+current_menu->lcd_window_pos].type)
        {
        case ENTRY_ONOFF:
                if(current_menu->entry_list[i+current_menu->lcd_window_pos].var1)
                    display_string(" On");
                else
                    display_string(" Off");
            break;
        case ENTRY_BIN:
                if(current_menu->entry_list[i+current_menu->lcd_window_pos].var1)
                    display_string(" 0");
                else
                    display_string(" 1");
            break;
        case ENTRY_BOOL:
                if(current_menu->entry_list[i+current_menu->lcd_window_pos].var1)
                    display_string(" T");
                else
                    display_string(" F");
            break;
        }

    }

    display_setcursor(0, current_menu->lcd_cursor_pos);
    display_data(current_menu->lcd_cursor_char);

    if(current_menu->lcd_window_pos > 0)
    {
        display_setcursor(current_menu->lcd_col_count-1, 0);
        display_data(current_menu->lcd_more_top_char);
    }

    if(current_menu->lcd_window_pos+current_menu->lcd_row_count < current_menu->entry_count)
    {
        display_setcursor(current_menu->lcd_col_count-1, current_menu->lcd_row_count-1);
        display_data(current_menu->lcd_more_down_char);
    }
}

void menu_set_entry_var1(MENU_STRUCT *menu, const uint8_t id, const uint8_t var1)
{
    for(int i=0; i<menu->entry_count; i++)
    {
        if(menu->entry_list[i].id == id)
        {
            menu->entry_list[i].var1 = var1;
            break;
        }
    }
}

uint8_t menu_get_entry_var1(MENU_STRUCT *menu, const uint8_t id)
{
    for(int i=0; i<menu->entry_count; i++)
    {
        if(menu->entry_list[i].id == id)
        {
            return menu->entry_list[i].var1;
        }
    }
    return 0;
}
